davecburke/auto-watch-cleaning-flask/Freecad/WatchCleaning/Jar_Holders/Version2/JarHoldersV2_Split-Slice.BR.stl

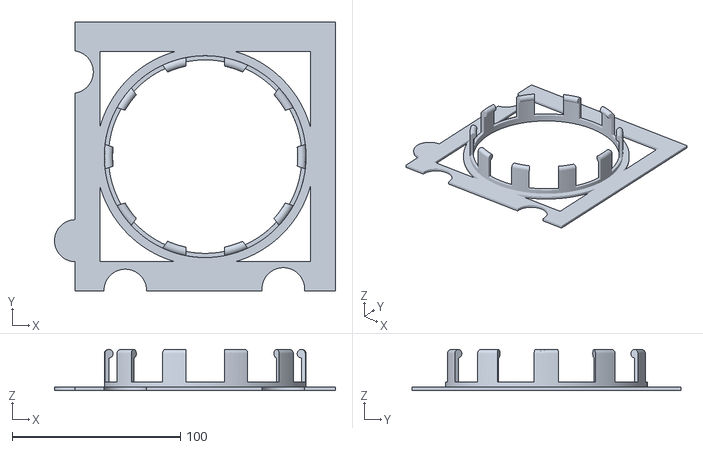
[picture p14: CAD file, 2023-11-11]
Freecad/WatchCleaning/Jar_Holders/Version2/JarHoldersV2_Split-Slice.BR.stl
167.1 x 159.8 x 24.5
