davecburke/auto-watch-cleaning-flask/Freecad/WatchCleaning/Jar_Holders/Version2/JarHoldersV2_PreSplit.FCStd

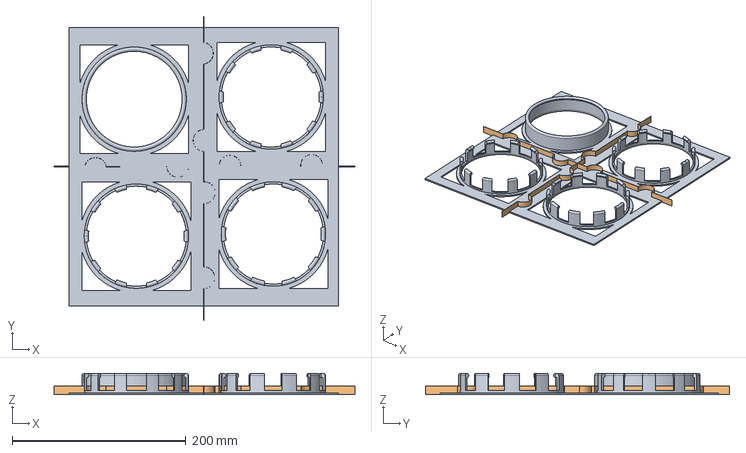
[picture p15: CAD file, 2023-11-11]
Freecad/WatchCleaning/Jar_Holders/Version2/JarHoldersV2_PreSplit.FCStd
346.0 x 350.0 x 24.5 mm
BuildPlate
Cutter
