davecburke/auto-watch-cleaning-flask/Freecad/WatchCleaning/Jar_Holders/Version2/JarHoldersV6_Heater_PreSplit.FCStd

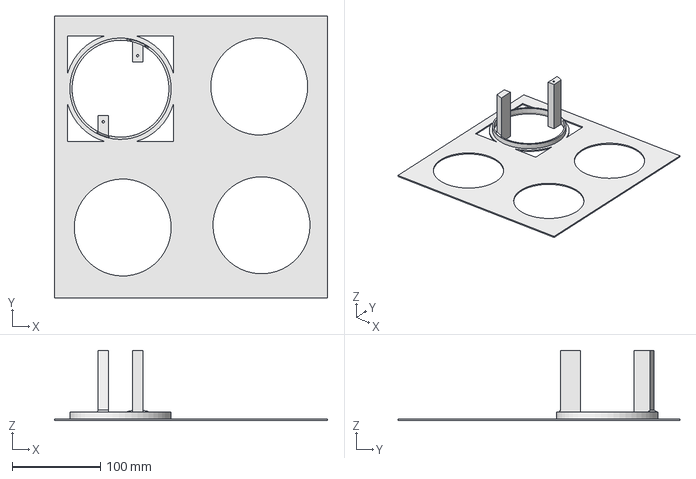
[picture p16: CAD file, 2023-11-11]
Freecad/WatchCleaning/Jar_Holders/Version2/JarHoldersV6_Heater_PreSplit.FCStd
310.0 x 320.0 x 80.0 mm
