davecburke/auto-watch-cleaning-flask/Freecad/WatchCleaning/Jar_Holders/Version2/JarHoldersV2_Split.FCStd

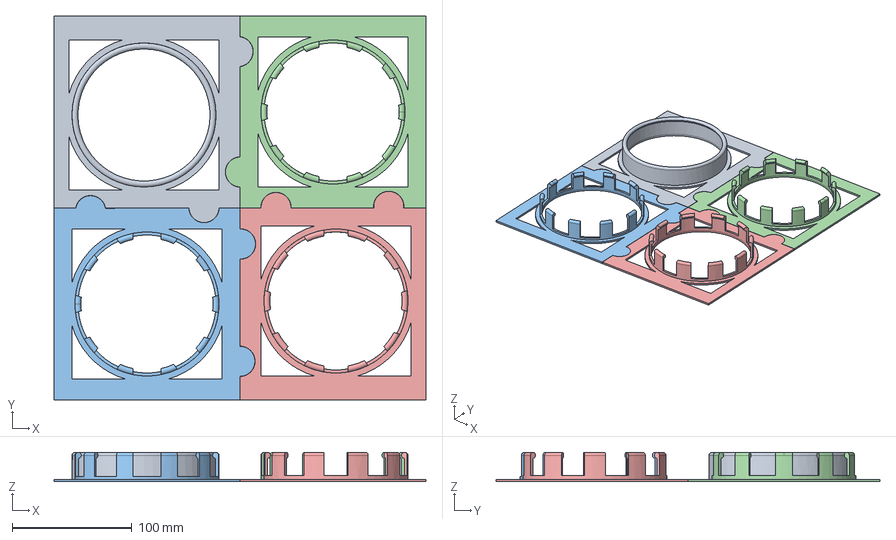
[picture p17: CAD file, 2023-11-11]
Freecad/WatchCleaning/Jar_Holders/Version2/JarHoldersV2_Split.FCStd
310.0 x 320.0 x 24.5 mm
Slice.BL
Slice.Cutter
Slice.FL
Slice.BR
Slice.FR
