davecburke/auto-watch-cleaning-flask/Freecad/WatchCleaning/Jar_Holders/Version2/JarHoldersV2_Split-Slice.FR.stl

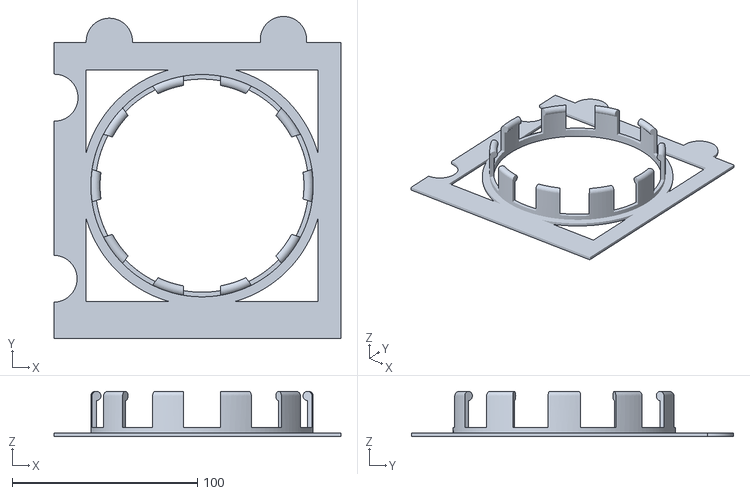
[picture p18: CAD file, 2023-11-11]
Freecad/WatchCleaning/Jar_Holders/Version2/JarHoldersV2_Split-Slice.FR.stl
154.9 x 173.8 x 24.5
