davecburke/auto-watch-cleaning-flask/Freecad/WatchCleaning/Jar_Holders/Version2/JarHoldersV6_Heater_PreSplit-BL.stl

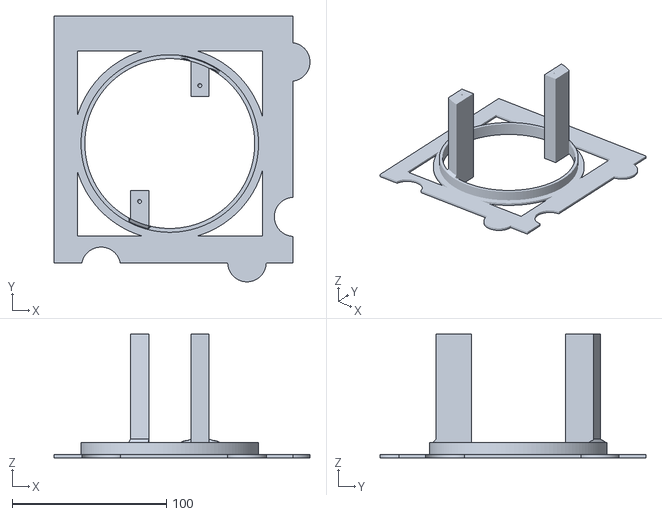
[picture p19: CAD file, 2023-11-11]
Freecad/WatchCleaning/Jar_Holders/Version2/JarHoldersV6_Heater_PreSplit-BL.stl
165.8 x 172.1 x 80.0
